afonsus1997/Duckuino/pics and renders/AlexDavis.bmp

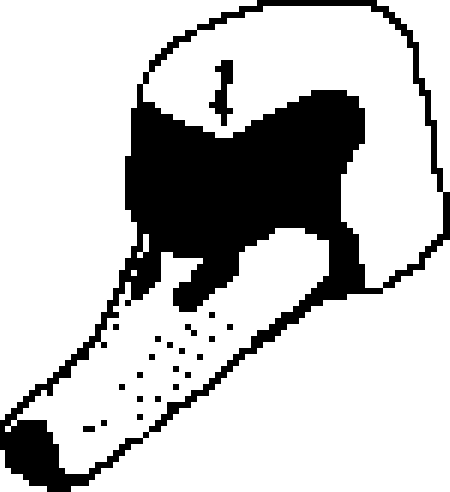
pics and renders/AlexDavis.bmp
