afonsus1997/Duckuino/pics and renders/AlexDavisinv.bmp

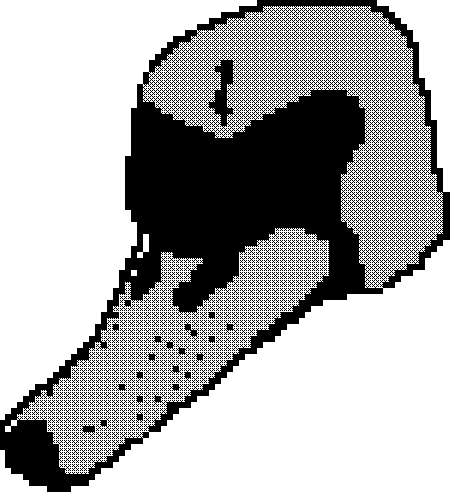
pics and renders/AlexDavisinv.bmp
