afonsus1997/Duckuino/pics and renders/silk2.bmp

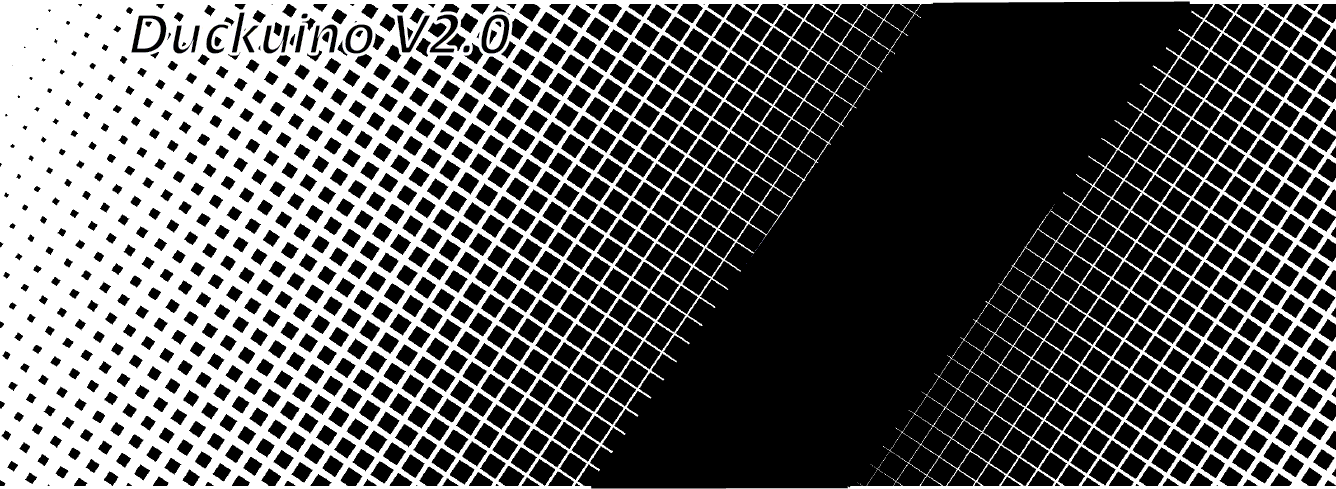
pics and renders/silk2.bmp
