afonsus1997/Duckuino/pics and renders/silk.bmp

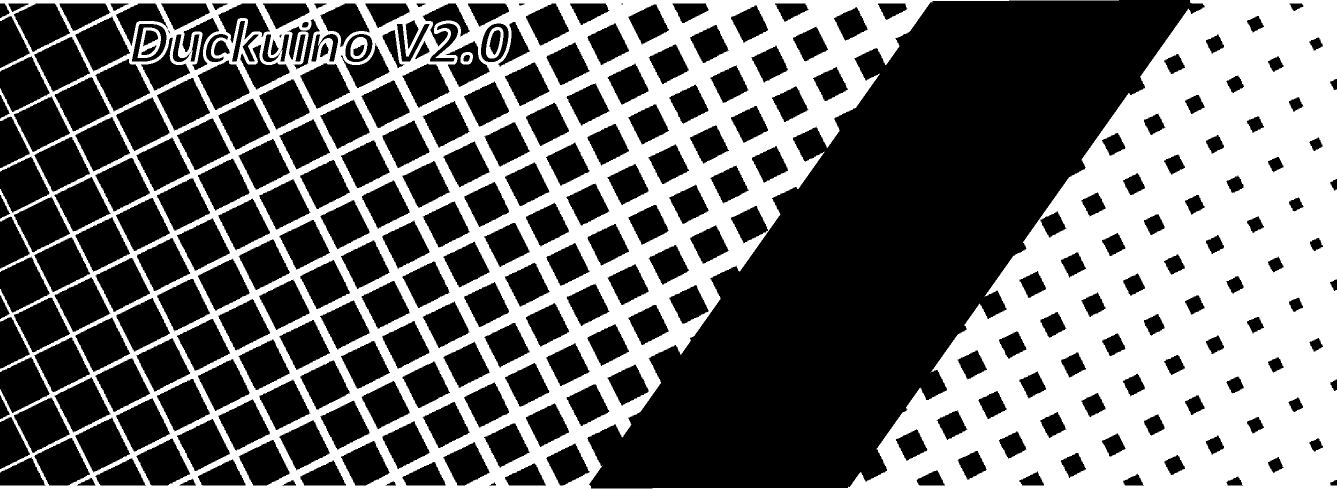
pics and renders/silk.bmp
