afonsus1997/Duckuino/Code/Firmware/pins.h

#ifndef PINS_h
#define PINS_h
#pragma once

#define dip1 9
#define dip2 10
#define dip3 13
#define dip4 5

#define led1 7
#define led2 6

#define left 12
#define right 11
#define center 8

#define blinkInterval 250
#endif
