afonsus1997/Duckuino/Code/Firmware/Menu.h

#pragma once

#ifndef MENU_h
#define MENU_h

#include <MenuSystem.h>
#include "oled.h";
#include "pins.h";
extern Cytron_SSD1306 oled;
//extern EEPROM;
void setupMenu();

void checkHardware();

#endif
